timshac/WekaHR/firmware/particle_gen3/src/print_json.h

void printIndent(size_t indent);
void printString(const char *str);
void printJsonInner(JsonParser &jp, const JsonParserGeneratorRK::jsmntok_t *container, size_t indent) ;
void printJson(JsonParser &jp);
